ZVV2/Crabsy/documentation/captures/7_crabsy_new_core.PNG

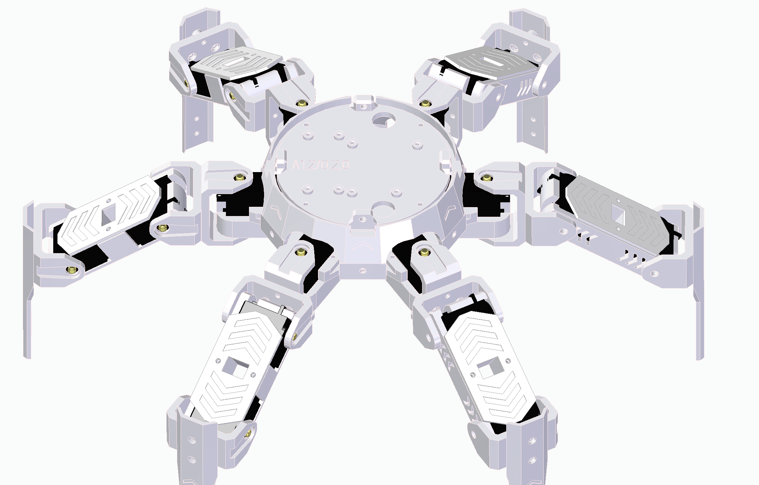
documentation/captures/7_crabsy_new_core.PNG
