ZVV2/Crabsy/documentation/captures/8_new_flanges.PNG

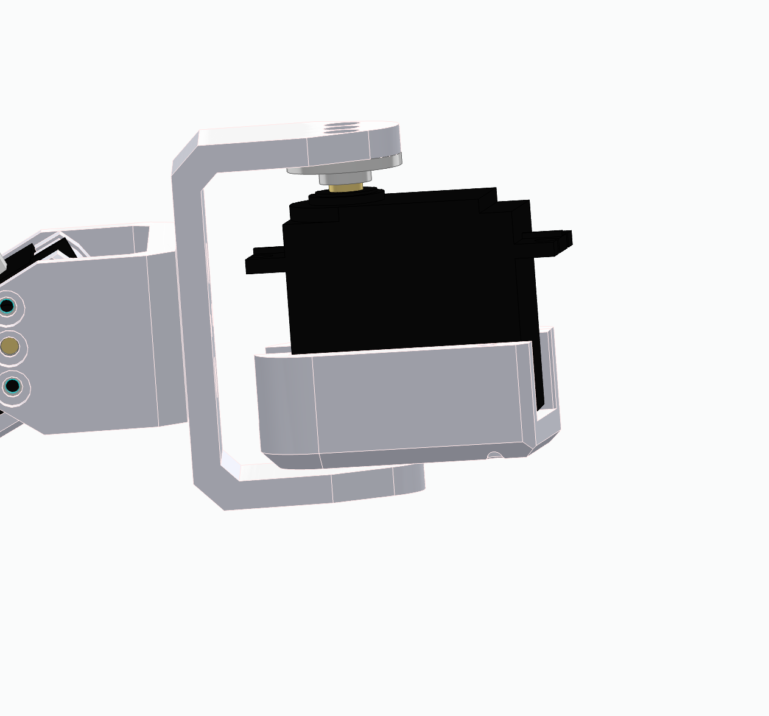
documentation/captures/8_new_flanges.PNG
