ZVV2/Crabsy/documentation/pictures/11_final_first_build_1.jpg

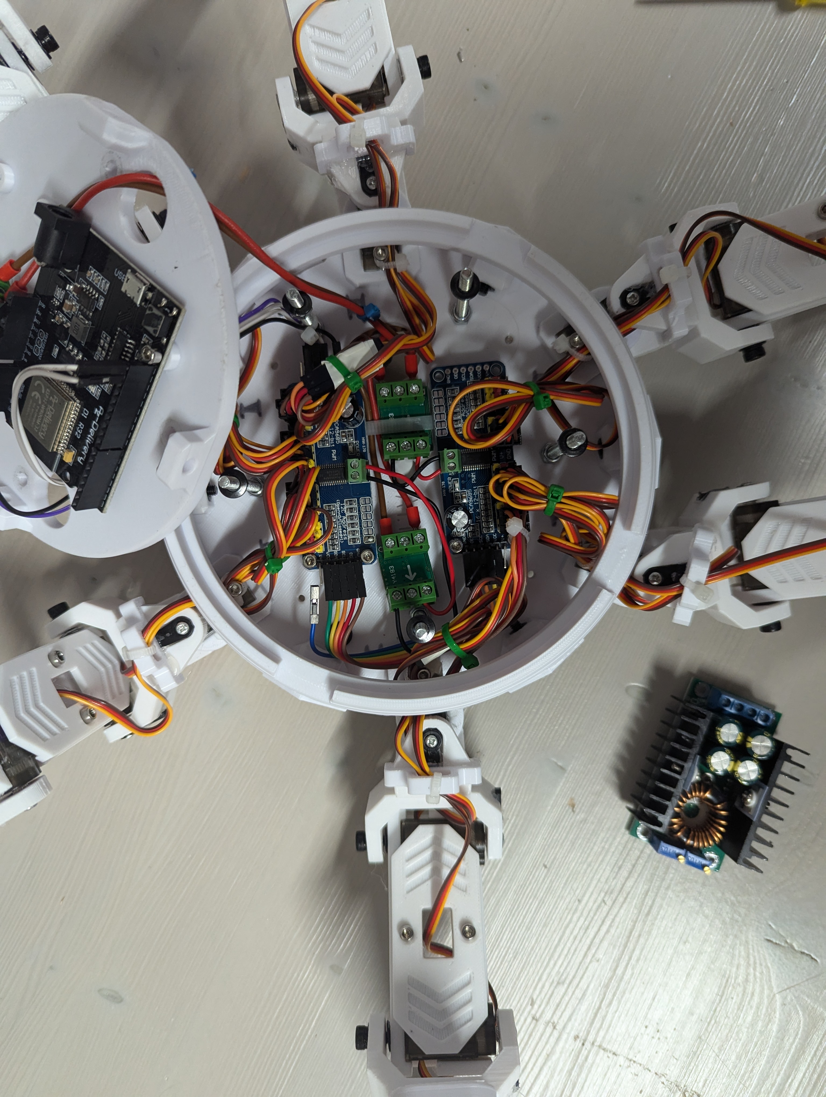
documentation/pictures/11_final_first_build_1.jpg
