ZVV2/Crabsy/documentation/pictures/12_final_first_build_2.jpg

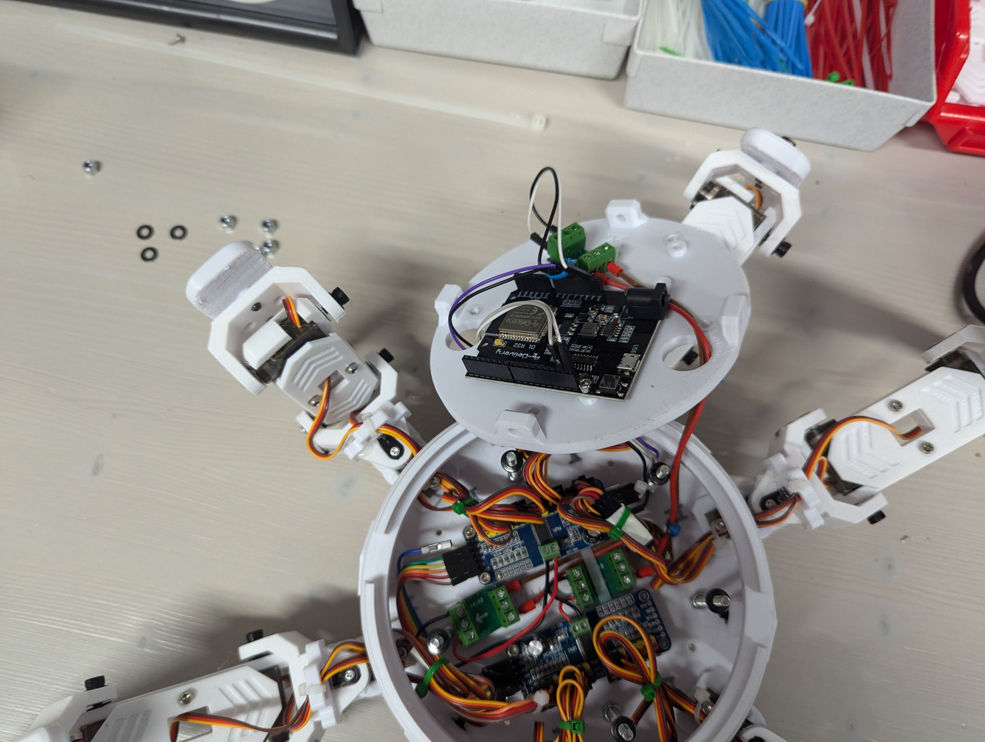
documentation/pictures/12_final_first_build_2.jpg
